EDrTech/ILM139C/docs/visual/ILM139C_asm_back_3d.png

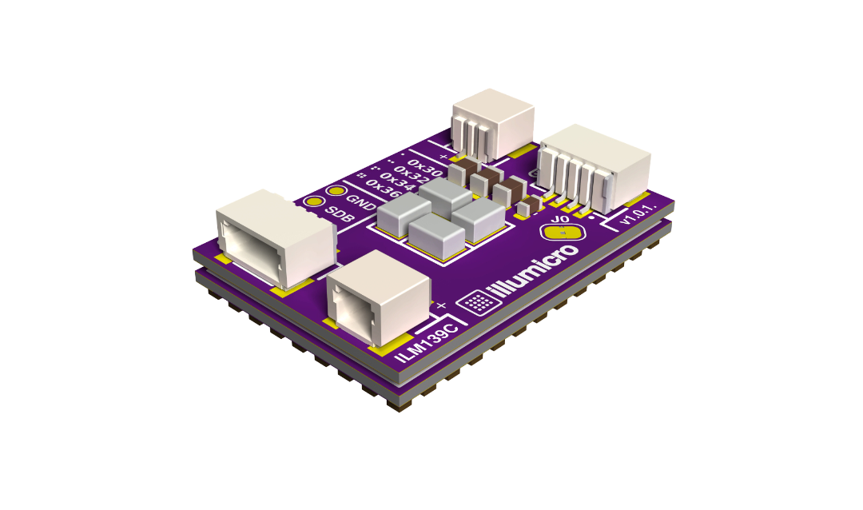
docs/visual/ILM139C_asm_back_3d.png
