EDrTech/ILM139C/docs/visual/ILM139C_bot.png

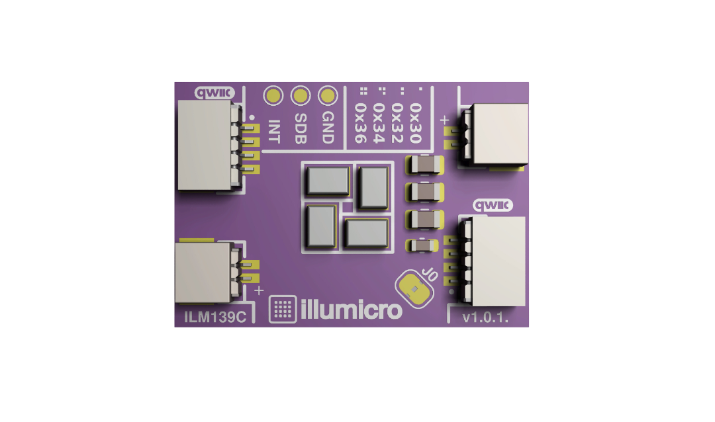
docs/visual/ILM139C_bot.png
