EDrTech/ILM139C/docs/visual/ILM139CD_bot.png

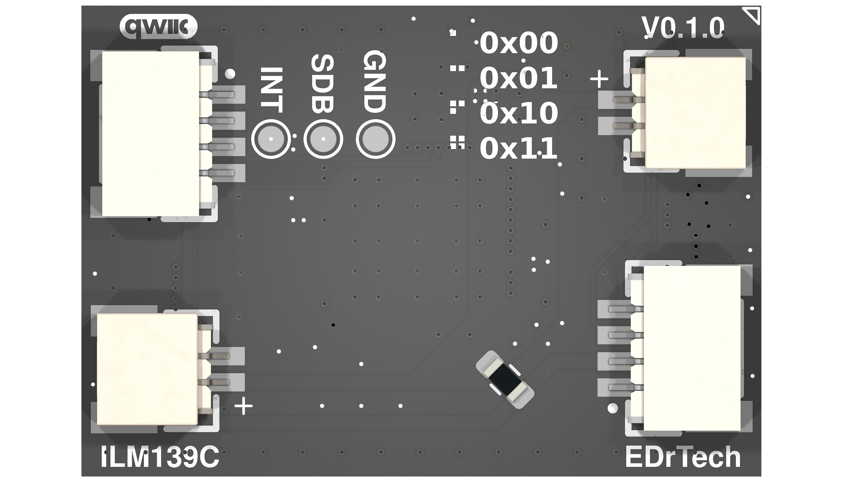
docs/visual/ILM139CD_bot.png
