EDrTech/ILM139C/docs/visual/ILM139CD_top.png

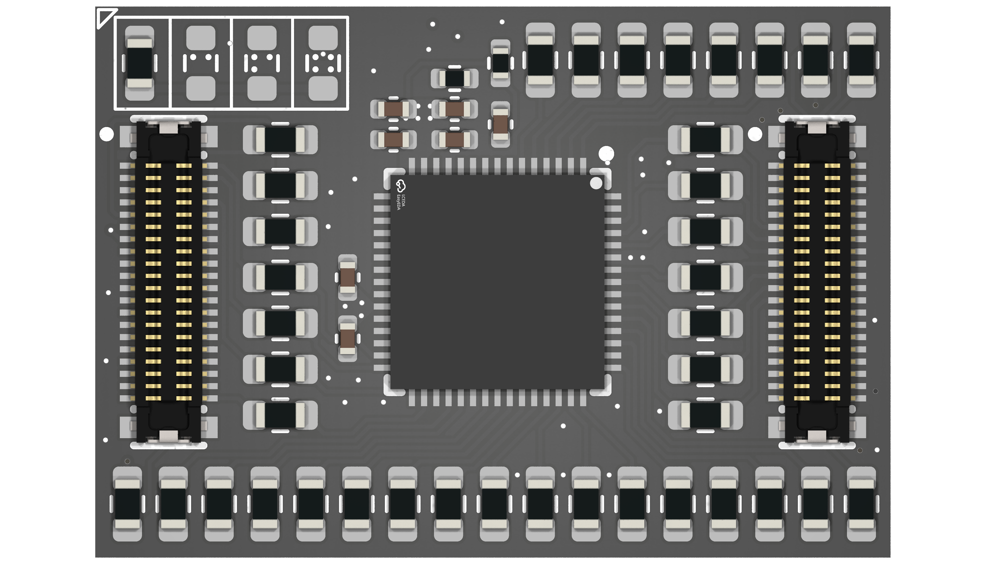
docs/visual/ILM139CD_top.png
