EDrTech/ILM139C/docs/visual/ILM139CM_bot.png

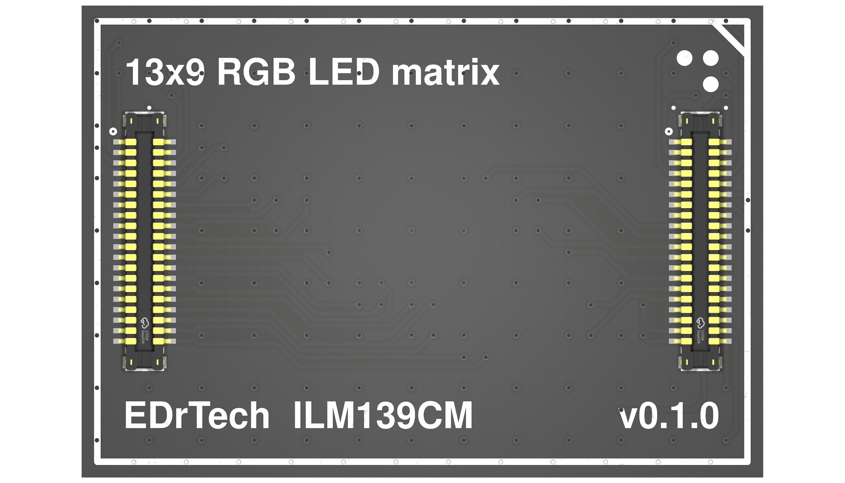
docs/visual/ILM139CM_bot.png
