EDrTech/ILM139C/docs/visual/ILM139CM_iso_3d_bot.png

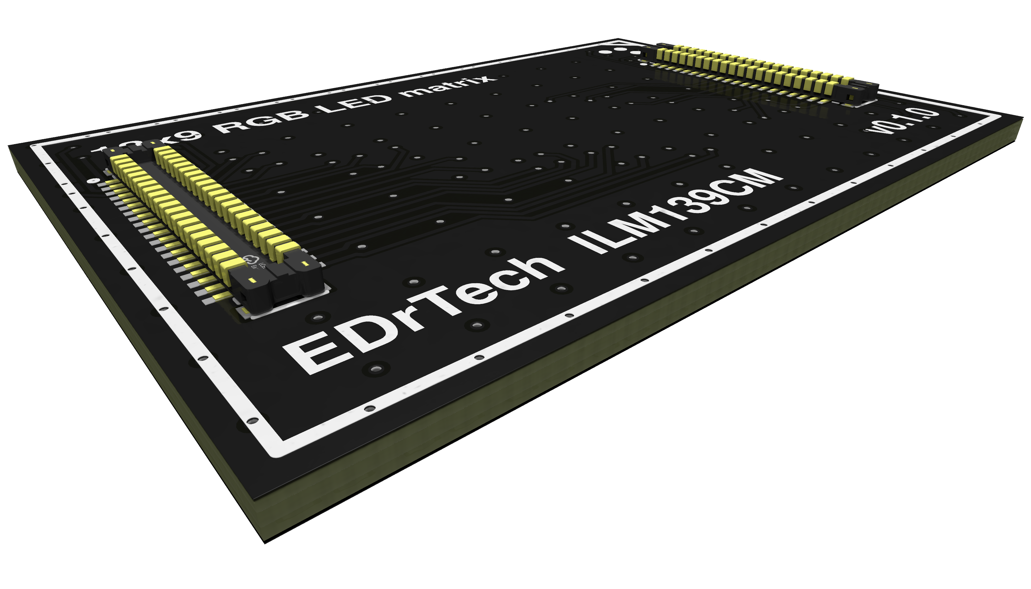
docs/visual/ILM139CM_iso_3d_bot.png
