EDrTech/ILM139C/docs/visual/ILM139CM_vert_3d_bot.png

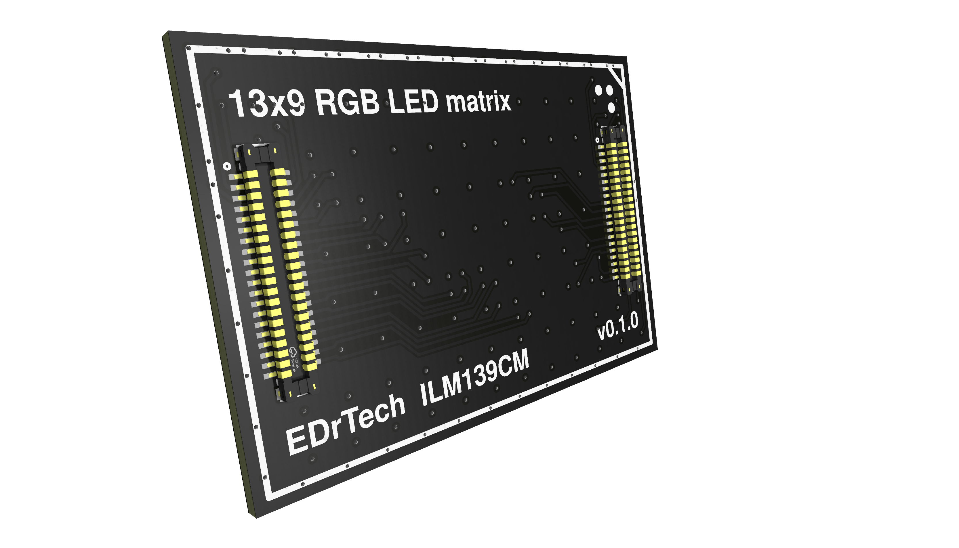
docs/visual/ILM139CM_vert_3d_bot.png
